MrViet1502/git-rfid-key/Firmware-PN532/src/card.cpp

#include "global.h"

bool isCardRegistered(byte *uid) // function check card is registered
{

    for (int i = 0; i < cardCount; i++)
    {
        bool match = true;
        for (int j = 0; j < 4; j++)
        {
            if (registeredCards[i].uid[j] != uid[j])
            {
                match = false;
                break;
            }
        }
        if (match)
        {
            return true;
        }
    }
    return false;
}

void storeCard(byte *uid) // function store card
{
    buzzerBeep(1, 500);
    // loadCardsFromEEPROM();
    if (cardCount == 0)
    {
        memcpy(registeredCards[cardCount].uid, uid, uidLength);
        registeredCards[cardCount].uidLength = uidLength;
    }
    else
    {
        if (cardCount < MAX_CARDS)
        {
            memcpy(registeredCards[cardCount].uid, uid, uidLength);
            registeredCards[cardCount].uidLength = uidLength;
            cardCount++;
            // Serial.print("New Card UID:");
            // for (byte i = 0; i < uid.size; i++)
            // {
            //     Serial.print(registeredCards[cardCount - 1].uid[i] < 0x10 ? " 0" : " ");
            //     Serial.print(registeredCards[cardCount - 1].uid[i], HEX);
            // }

            saveCardsToEEPROM();
            Serial.println();
        }
    }
}

void removeCard(byte *uid) // function remove card
{
    // loadCardsFromEEPROM();
    for (int i = 1; i < cardCount; i++)
    {
        bool match = true;
        for (int j = 0; j < 4; j++)
        {
            if (registeredCards[i].uid[j] != uid[j])
            {
                match = false;
                break;
            }
        }
        if (match)
        {
            // Move the remaining cards up to fill the empty space
            for (int k = i; k < cardCount - 1; k++)
            {
                for (int j = 0; j < 4; j++)
                {
                    registeredCards[k].uid[j] = registeredCards[k + 1].uid[j];
                }
            }
            cardCount--;
            // Serial.print("Card UID removed:");
            // for (byte i = 0; i < 4; i++)
            // {
            //     Serial.print(uid[i] < 0x10 ? " 0" : " ");
            //     Serial.print(uid[i], HEX);
            // }
            saveCardsToEEPROM();
            Serial.println();
            buzzerBeep(2, 500);
        }
    }
}

void removeAll()
{

    cardCount = 1;
    for (int i = 1; i < MAX_CARDS; i++)
    {
        for (int j = 0; j < 4; j++)
        {
            registeredCards[i].uid[j] = 0;
        }
    }
    saveCardsToEEPROM();
    // Serial.println("All cards removed");
    exitSetupMode(); // exit setupmode
}

bool isMasterCard(byte *uid)
{
    for (int i = 0; i < 4; i++)
    {
        if (registeredCards[0].uid[i] != uid[i])
        {
            return false;
        }
    }
    return true;
}

bool readNFC()
{
    if (nfc.tagPresent())
    {
        Serial.println("Tag waiting..");
        NfcTag tag = nfc.read();
        tag.print();

        // byte uid[10]; // Tăng kích thước mảng để chứa UID dài hơn nếu cần
        uidLength = tag.getUidLength();
        tag.getUid(uid, sizeof(uid));

        // for (int i = 0; i < 4; i++)
        // {
        //   if (registeredCards[i].uidLength == 0) // Kiểm tra nếu vị trí chưa có thẻ nào
        //   {
        //     memcpy(registeredCards[i].uid, uid, uidLength);
        //     registeredCards[i].uidLength = uidLength;
        //     Serial.print("Stored UID in slot ");
        //     Serial.println(i);
        //     cardCount++;
        //     break;
        //   }
        // }

        return true;
    }
    return false;
}
