MrViet1502/git-rfid-key/Firmware-PN532/include/button.h

#ifndef BUTTON_H
#define BUTTON_H

void pressButtonRForOpenAndClose();
bool isSetupModeActive();
void checkButtonRemoveAll();
bool isHoldForOpen();
void checkButtonRForSetupMode();

#endif // BUTTON_H
